graulex/TER_Chademo/Code/IHM/schema_etats.jpg

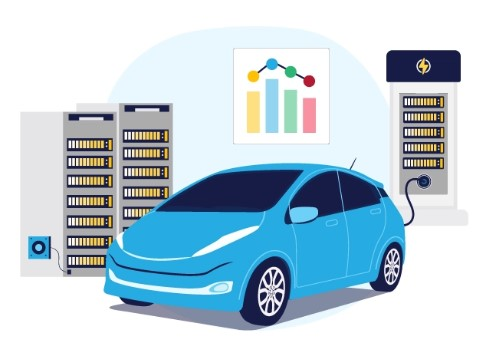
Code/IHM/schema_etats.jpg
