graulex/TER_Chademo/Diagrammes UML/Diagramme de classes EVSE.png

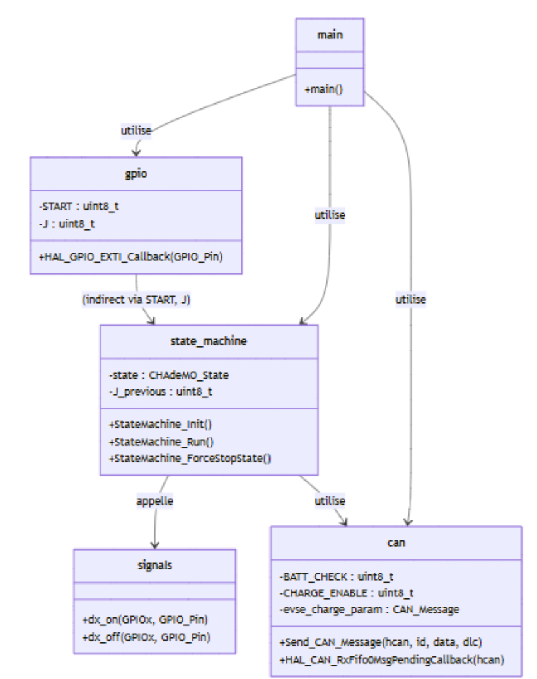
Diagrammes UML/Diagramme de classes EVSE.png
