graulex/TER_Chademo/Diagrammes UML/Diagramme de contexte.png

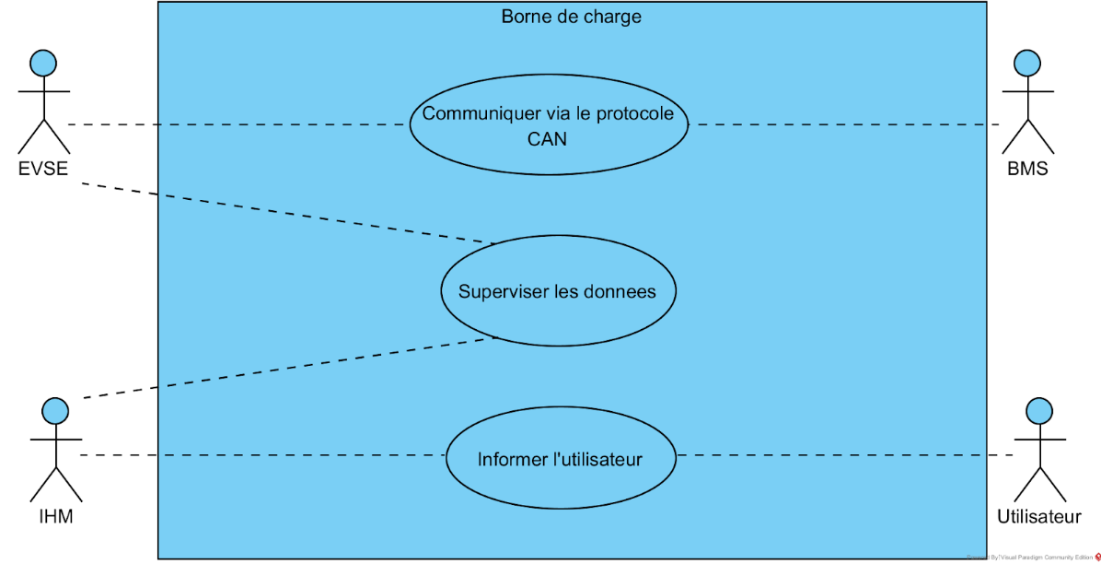
Diagrammes UML/Diagramme de contexte.png
