graulex/TER_Chademo/Diagrammes UML/Diagramme de séquence EV.png

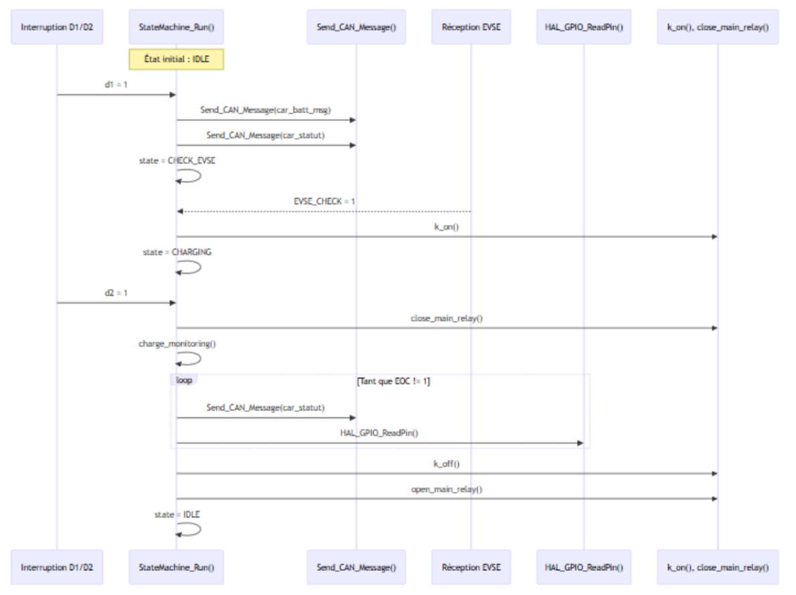
Diagrammes UML/Diagramme de séquence EV.png
