graulex/TER_Chademo/Diagrammes UML/Diagramme de séquence EVSE.png

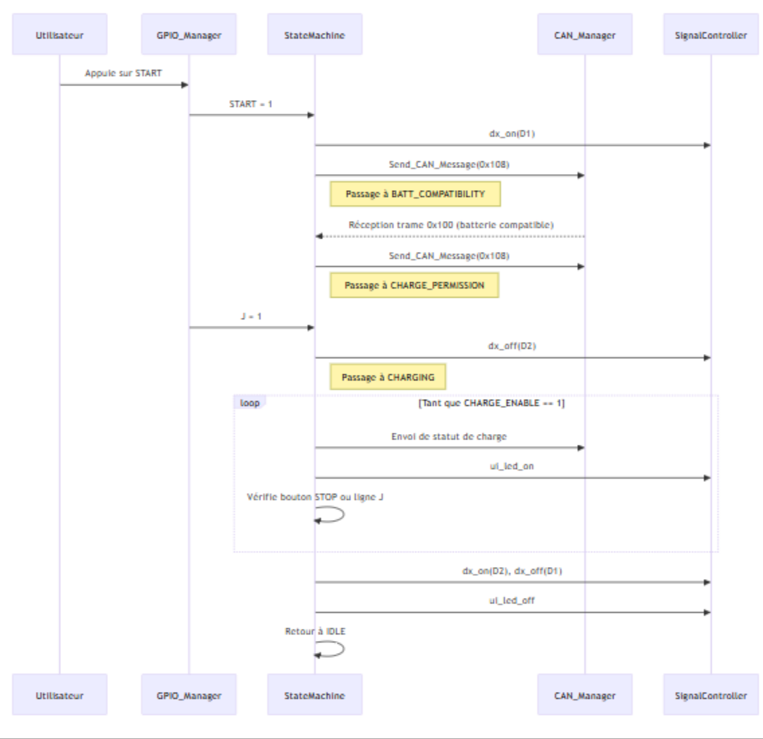
Diagrammes UML/Diagramme de séquence EVSE.png
