graulex/TER_Chademo/Diagrammes UML/Diagramme de séquence IHM.png

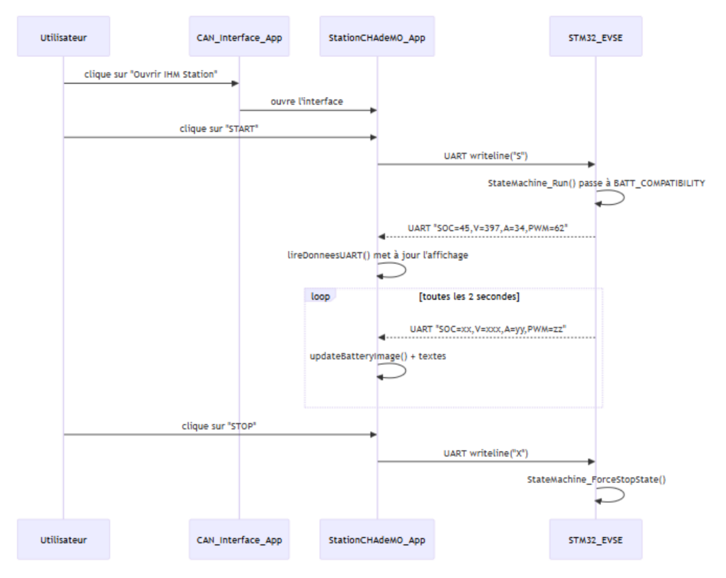
Diagrammes UML/Diagramme de séquence IHM.png
