graulex/TER_Chademo/Diagrammes UML/MEF_borne.jpg

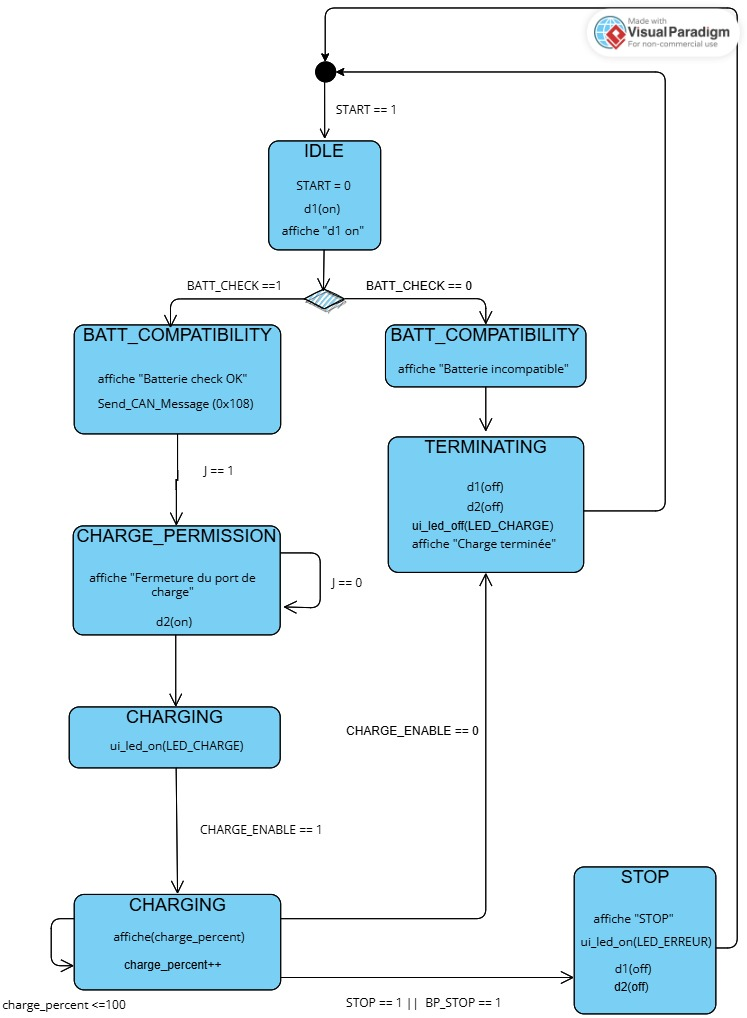
Diagrammes UML/MEF_borne.jpg
