graulex/TER_Chademo/Diagrammes UML/MEF_vehicule.jpg

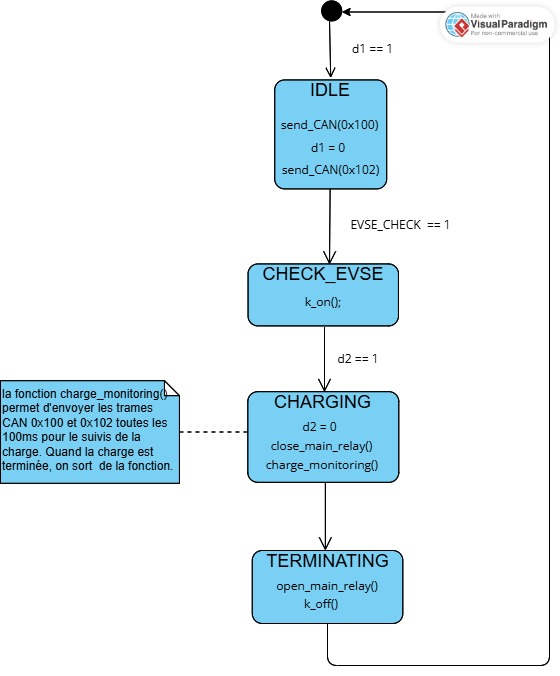
Diagrammes UML/MEF_vehicule.jpg
