graulex/TER_Chademo/Code/Borne/Src/usart.c

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
/* Includes ------------------------------------------------------------------*/
#include "usart.h"

/* USER CODE BEGIN 0 */
uint8_t rx_data;             // Variable pour stocker l'octet reçu par interruption
volatile uint8_t STOP1 = 0;  // Drapeau utilisé pour arrêter la charge manuellement
/* USER CODE END 0 */

UART_HandleTypeDef huart2;

/* USART2 init function */
void MX_USART2_UART_Init(void)
{
  // Configuration des paramètres UART2 (vitesse, format, etc.)
  huart2.Instance = USART2;
  huart2.Init.BaudRate = 115200;
  huart2.Init.WordLength = UART_WORDLENGTH_8B;
  huart2.Init.StopBits = UART_STOPBITS_1;
  huart2.Init.Parity = UART_PARITY_NONE;
  huart2.Init.Mode = UART_MODE_TX_RX;
  huart2.Init.HwFlowCtl = UART_HWCONTROL_NONE;
  huart2.Init.OverSampling = UART_OVERSAMPLING_16;
  huart2.Init.OneBitSampling = UART_ONE_BIT_SAMPLE_DISABLE;
  huart2.AdvancedInit.AdvFeatureInit = UART_ADVFEATURE_NO_INIT;

  // Si erreur à l'initialisation, appel de Error_Handler()
  if (HAL_UART_Init(&huart2) != HAL_OK)
  {
    Error_Handler();
  }

}

void HAL_UART_MspInit(UART_HandleTypeDef* uartHandle)
{
  GPIO_InitTypeDef GPIO_InitStruct = {0};
  RCC_PeriphCLKInitTypeDef PeriphClkInit = {0};

  if(uartHandle->Instance==USART2)
  {
    // Sélection de la source d'horloge pour USART2
    PeriphClkInit.PeriphClockSelection = RCC_PERIPHCLK_USART2;
    PeriphClkInit.Usart2ClockSelection = RCC_USART2CLKSOURCE_PCLK1;

    if (HAL_RCCEx_PeriphCLKConfig(&PeriphClkInit) != HAL_OK)
    {
      Error_Handler();
    }

    // Activation de l'horloge USART2
    __HAL_RCC_USART2_CLK_ENABLE();

    // Activation de l'horloge GPIOA (pour les broches TX et RX)
    __HAL_RCC_GPIOA_CLK_ENABLE();

    /** Configuration des broches USART2 :
        PA2 -> TX
        PA3 -> RX
    */
    GPIO_InitStruct.Pin = USART_TX_Pin|USART_RX_Pin;
    GPIO_InitStruct.Mode = GPIO_MODE_AF_PP;
    GPIO_InitStruct.Pull = GPIO_NOPULL;
    GPIO_InitStruct.Speed = GPIO_SPEED_FREQ_VERY_HIGH;
    GPIO_InitStruct.Alternate = GPIO_AF7_USART2;
    HAL_GPIO_Init(GPIOA, &GPIO_InitStruct);

    // Initialisation de l’interruption USART2
    HAL_NVIC_SetPriority(USART2_IRQn, 1, 0);
    HAL_NVIC_EnableIRQ(USART2_IRQn);

  }
}

void HAL_UART_MspDeInit(UART_HandleTypeDef* uartHandle)
{
  if(uartHandle->Instance==USART2)
  {
    // Désactivation de l'horloge USART2
    __HAL_RCC_USART2_CLK_DISABLE();

    // Libération des broches GPIO utilisées par USART2
    HAL_GPIO_DeInit(GPIOA, USART_TX_Pin|USART_RX_Pin);

    // Désactivation de l'interruption USART2
    HAL_NVIC_DisableIRQ(USART2_IRQn);

  }
}

/* USER CODE BEGIN 1 */

// Callback déclenché à la réception d’un octet via USART2
void HAL_UART_RxCpltCallback(UART_HandleTypeDef *huart) {
    if (huart->Instance == USART2) {

        // Si caractère 'S' envoyé par Matlab est reçu → passage à l’état START
        if (rx_data == 'S') {
            START = 1;
        }

        // Si caractère 'X' envoyé par Matlab est reçu → arrêt d'urgence
        else if (rx_data == 'X') {
            STOP1 = 1;
        }

        // Réarmement de la réception UART en interruption pour recevoir le prochain octet
        HAL_UART_Receive_IT(&huart2, &rx_data, 1);
    }
}
/* USER CODE END 1 */
