graulex/TER_Chademo/Code/Vehicule/Src/gpio.c

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

/* Includes ------------------------------------------------------------------*/
#include "gpio.h"

/* USER CODE BEGIN 0 */

/*------------------------------------------------------------------------*/
/*Définition des variables d'états de d1 et d2
/*------------------------------------------------------------------------*/

volatile uint8_t d1 = 0;
volatile uint8_t d2 = 0;

/* USER CODE END 0 */

/*----------------------------------------------------------------------------*/
/* Configure GPIO                                                             */
/*----------------------------------------------------------------------------*/
/** Configure pins as
        * Analog
        * Input
        * Output
        * EVENT_OUT
        * EXTI
*/
void MX_GPIO_Init(void)
{

  GPIO_InitTypeDef GPIO_InitStruct = {0};

  /* GPIO Ports Clock Enable */
  __HAL_RCC_GPIOC_CLK_ENABLE();
  __HAL_RCC_GPIOH_CLK_ENABLE();
  __HAL_RCC_GPIOA_CLK_ENABLE();
  __HAL_RCC_GPIOB_CLK_ENABLE();

  /*Configure GPIO pin Output Level */
  HAL_GPIO_WritePin(LD2_GPIO_Port, LD2_Pin, GPIO_PIN_RESET);

  /*Configure GPIO pin Output Level */
  HAL_GPIO_WritePin(main_relay_GPIO_Port, main_relay_Pin, GPIO_PIN_SET);

  /*Configure GPIO pin Output Level */
  HAL_GPIO_WritePin(k_GPIO_Port, k_Pin, GPIO_PIN_RESET);

  /*Configure GPIO pin : B1_Pin */
  GPIO_InitStruct.Pin = B1_Pin;
  GPIO_InitStruct.Mode = GPIO_MODE_IT_FALLING;
  GPIO_InitStruct.Pull = GPIO_NOPULL;
  HAL_GPIO_Init(B1_GPIO_Port, &GPIO_InitStruct);

  /*Configure GPIO pins : LD2_Pin main_relay_Pin */
  GPIO_InitStruct.Pin = LD2_Pin|main_relay_Pin;
  GPIO_InitStruct.Mode = GPIO_MODE_OUTPUT_PP;
  GPIO_InitStruct.Pull = GPIO_NOPULL;
  GPIO_InitStruct.Speed = GPIO_SPEED_FREQ_LOW;
  HAL_GPIO_Init(GPIOA, &GPIO_InitStruct);

  /*Configure GPIO pin : d1_Pin */
  GPIO_InitStruct.Pin = d1_Pin;
  GPIO_InitStruct.Mode = GPIO_MODE_IT_FALLING;
  GPIO_InitStruct.Pull = GPIO_PULLUP;
  HAL_GPIO_Init(d1_GPIO_Port, &GPIO_InitStruct);

  /*Configure GPIO pin : d2_Pin */
  GPIO_InitStruct.Pin = d2_Pin;
  GPIO_InitStruct.Mode = GPIO_MODE_IT_FALLING;
  GPIO_InitStruct.Pull = GPIO_PULLUP;
  HAL_GPIO_Init(d2_GPIO_Port, &GPIO_InitStruct);

  /*Configure GPIO pin : k_Pin */
  GPIO_InitStruct.Pin = k_Pin;
  GPIO_InitStruct.Mode = GPIO_MODE_OUTPUT_PP;
  GPIO_InitStruct.Pull = GPIO_NOPULL;
  GPIO_InitStruct.Speed = GPIO_SPEED_FREQ_LOW;
  HAL_GPIO_Init(k_GPIO_Port, &GPIO_InitStruct);

  /* EXTI interrupt init*/
  HAL_NVIC_SetPriority(EXTI4_IRQn, 1, 0);
  HAL_NVIC_EnableIRQ(EXTI4_IRQn);

  HAL_NVIC_SetPriority(EXTI9_5_IRQn, 1, 0);
  HAL_NVIC_EnableIRQ(EXTI9_5_IRQn);

}

/* USER CODE BEGIN 2 */

/*------------------------------------------------------------------------*/
/*Callback de l'interruption des pins D1 et D2							   */
/*------------------------------------------------------------------------*/

void HAL_GPIO_EXTI_Callback(uint16_t GPIO_Pin) {
    if (GPIO_Pin == GPIO_PIN_6) {  // Vérifie si c'est PC0 qui a déclenché l'interruption
        d1 = 1;  // Active le flag de d1
    }
    else if (GPIO_Pin == GPIO_PIN_4){
    	d2 = 1;
    }
}


/* USER CODE END 2 */
